tamran/Team-Hydra-II/2-14-17/blueVsConc.png

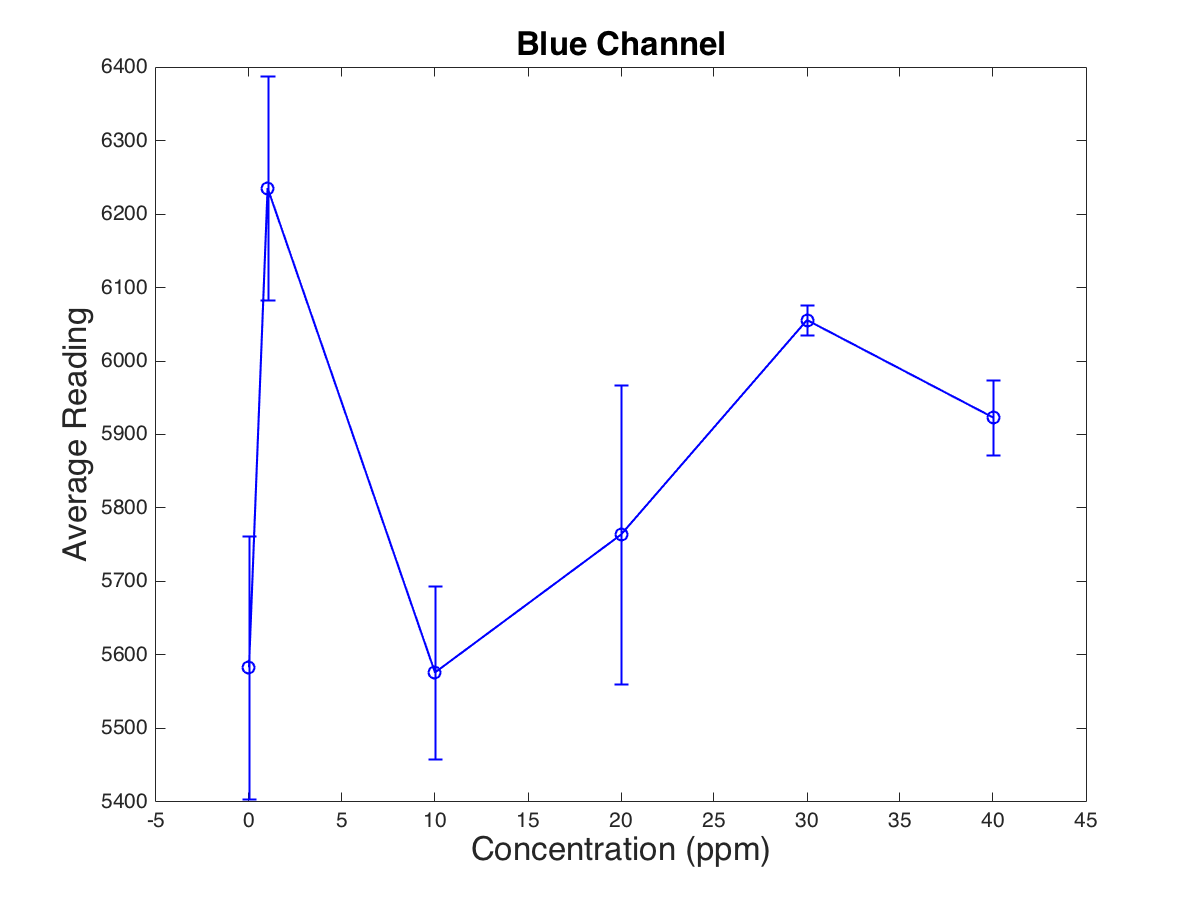
2-14-17/blueVsConc.png
