tamran/Team-Hydra-II/2-14-17/blueVsTime.png

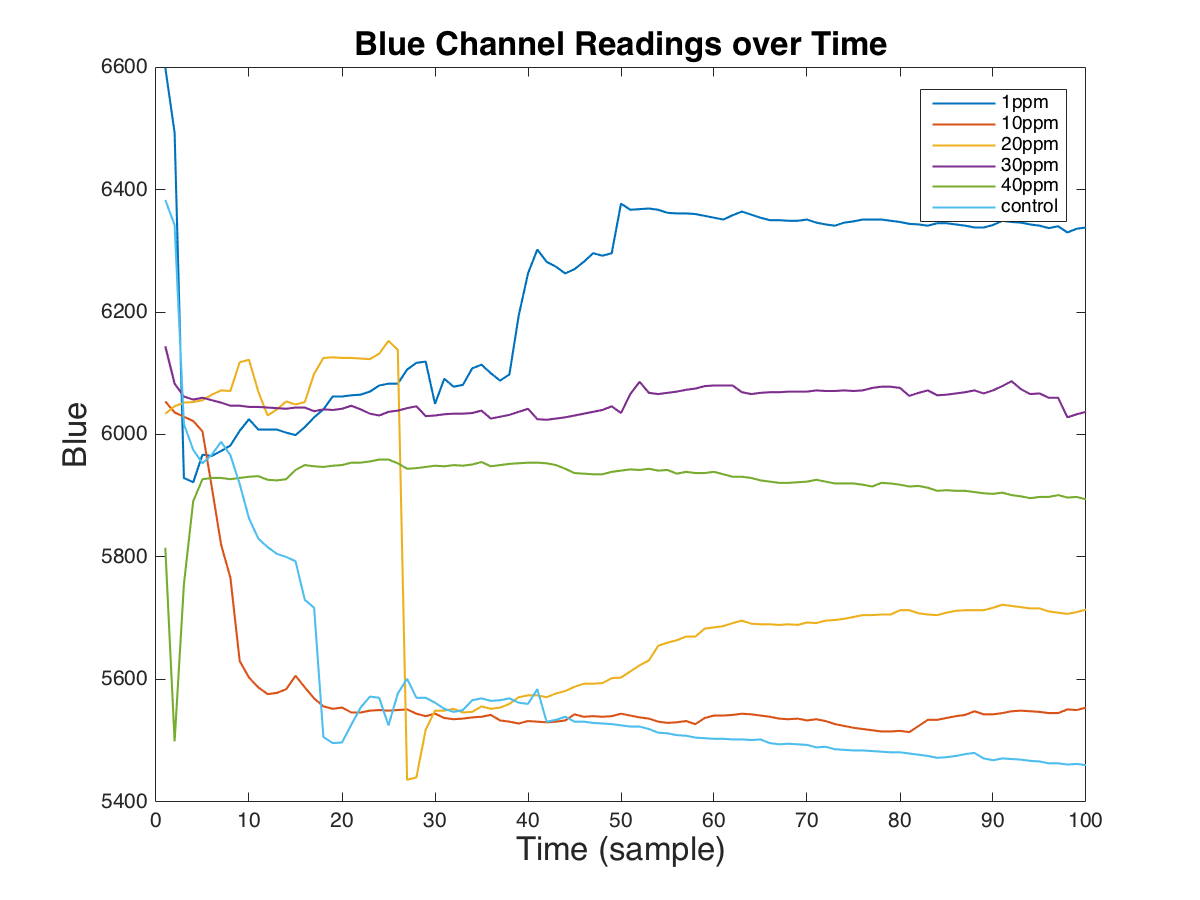
2-14-17/blueVsTime.png
