tamran/Team-Hydra-II/2-14-17/clearVsConc.png

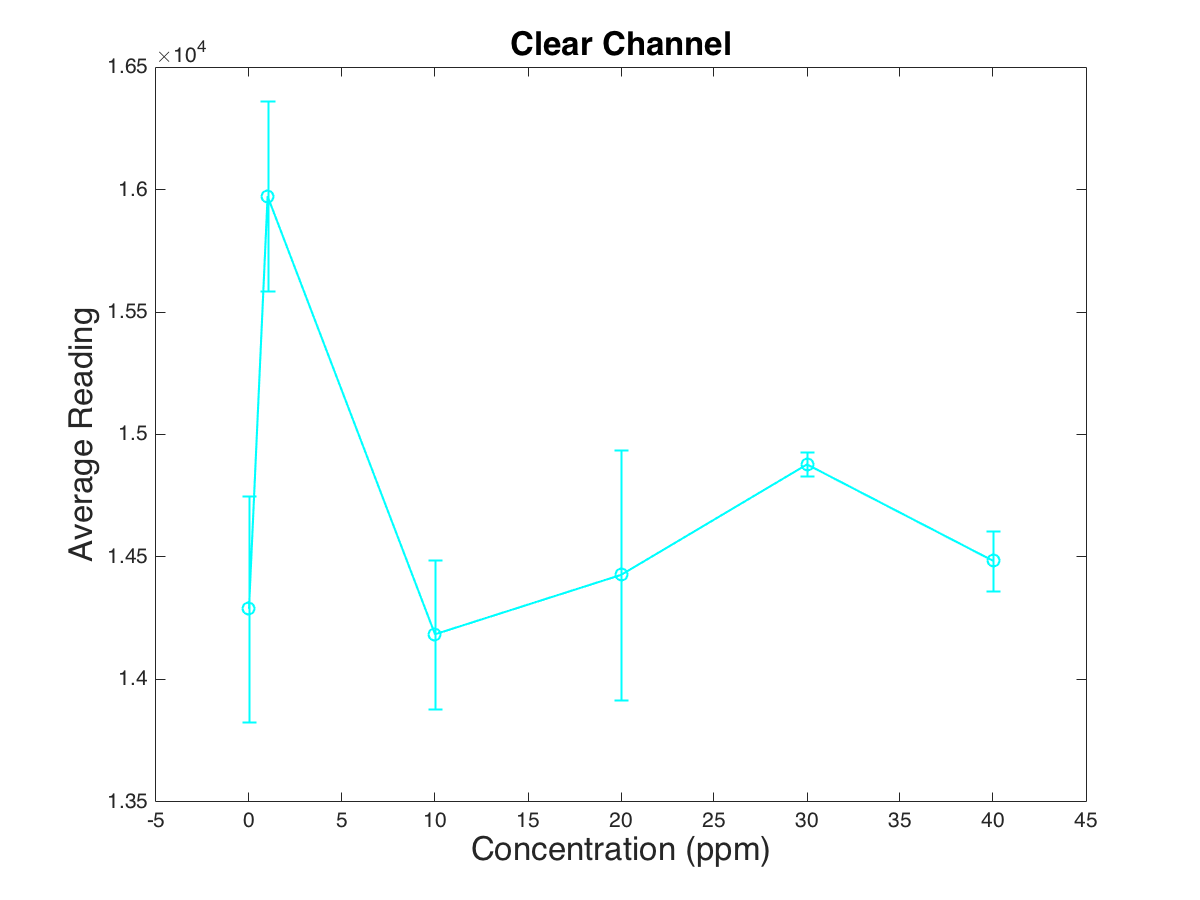
2-14-17/clearVsConc.png
