tamran/Team-Hydra-II/2-14-17/clearVsTime.png

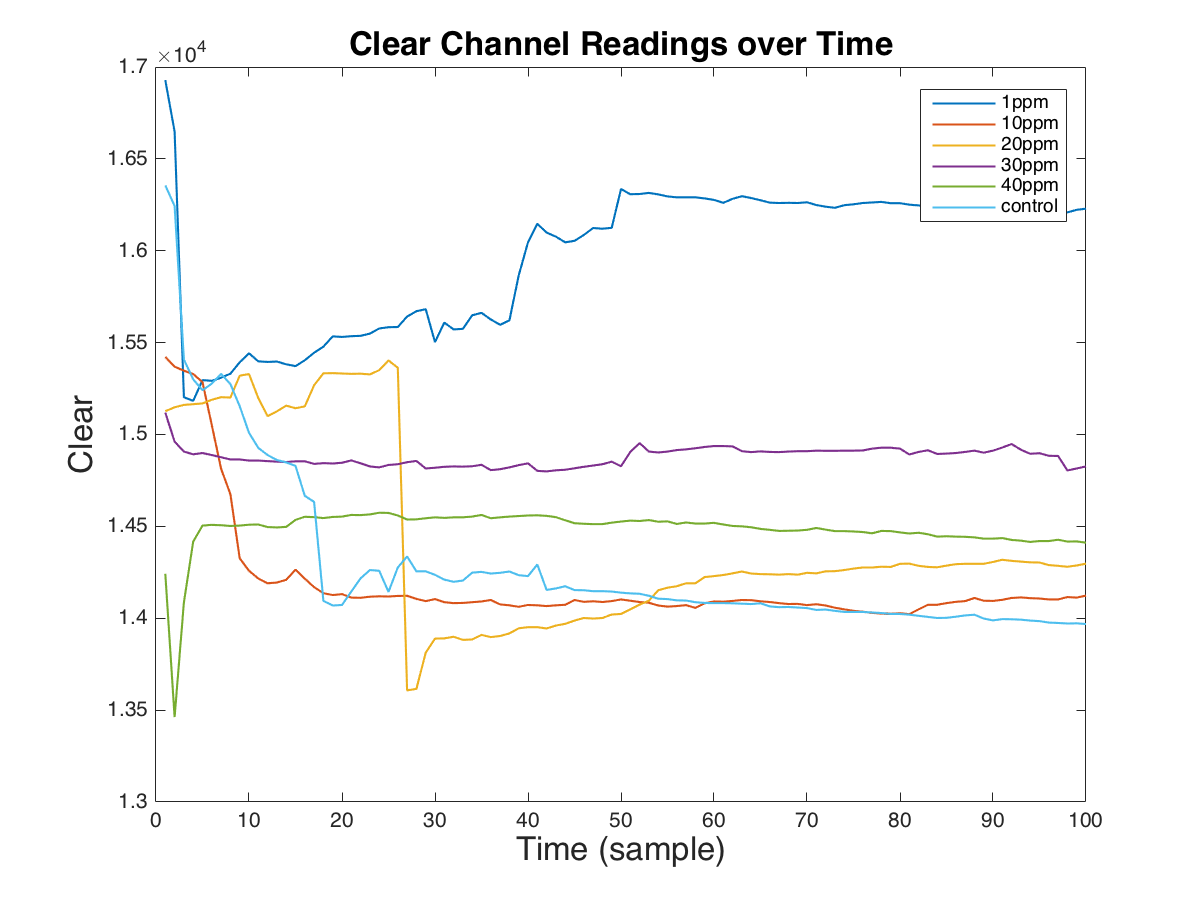
2-14-17/clearVsTime.png
