tamran/Team-Hydra-II/2-14-17/colorTempVsConc.png

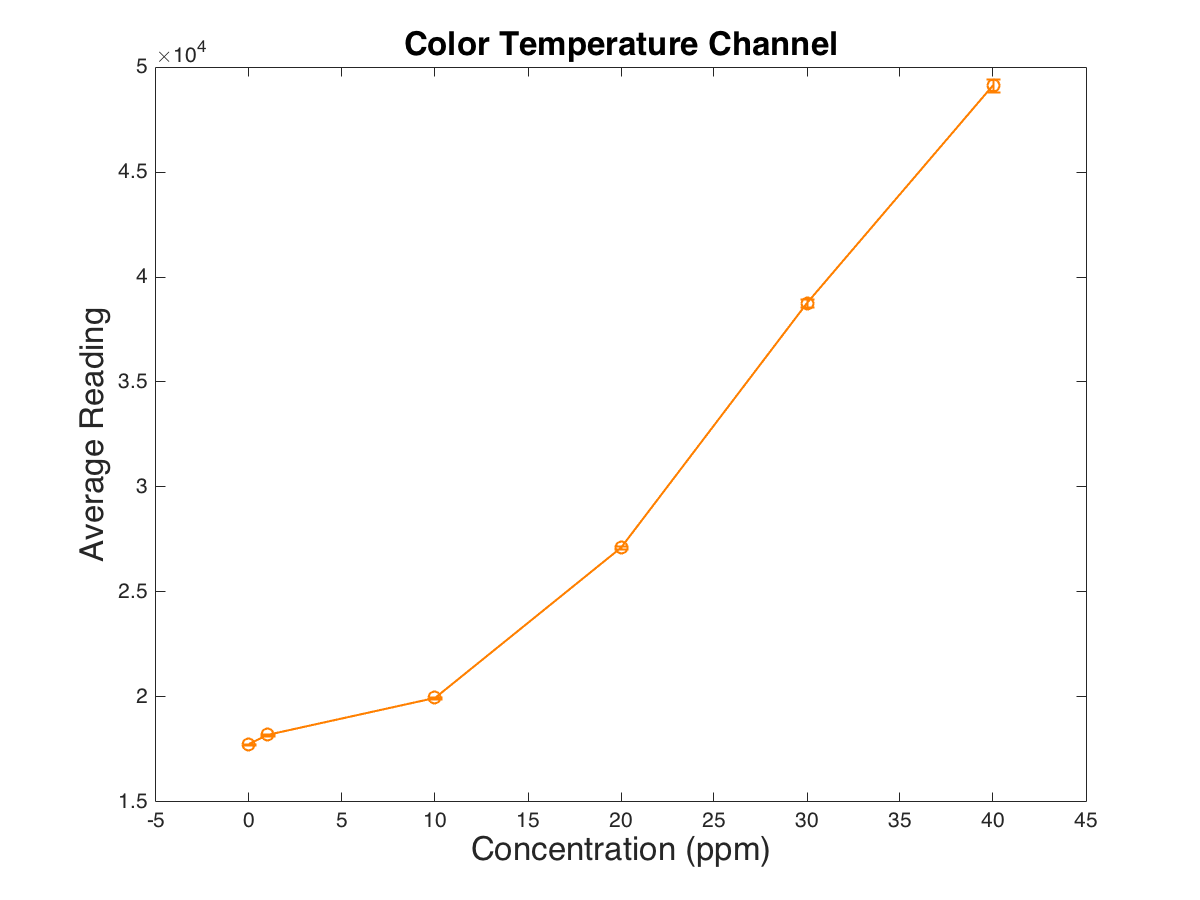
2-14-17/colorTempVsConc.png
