tamran/Team-Hydra-II/2-14-17/cTempVsTime.png

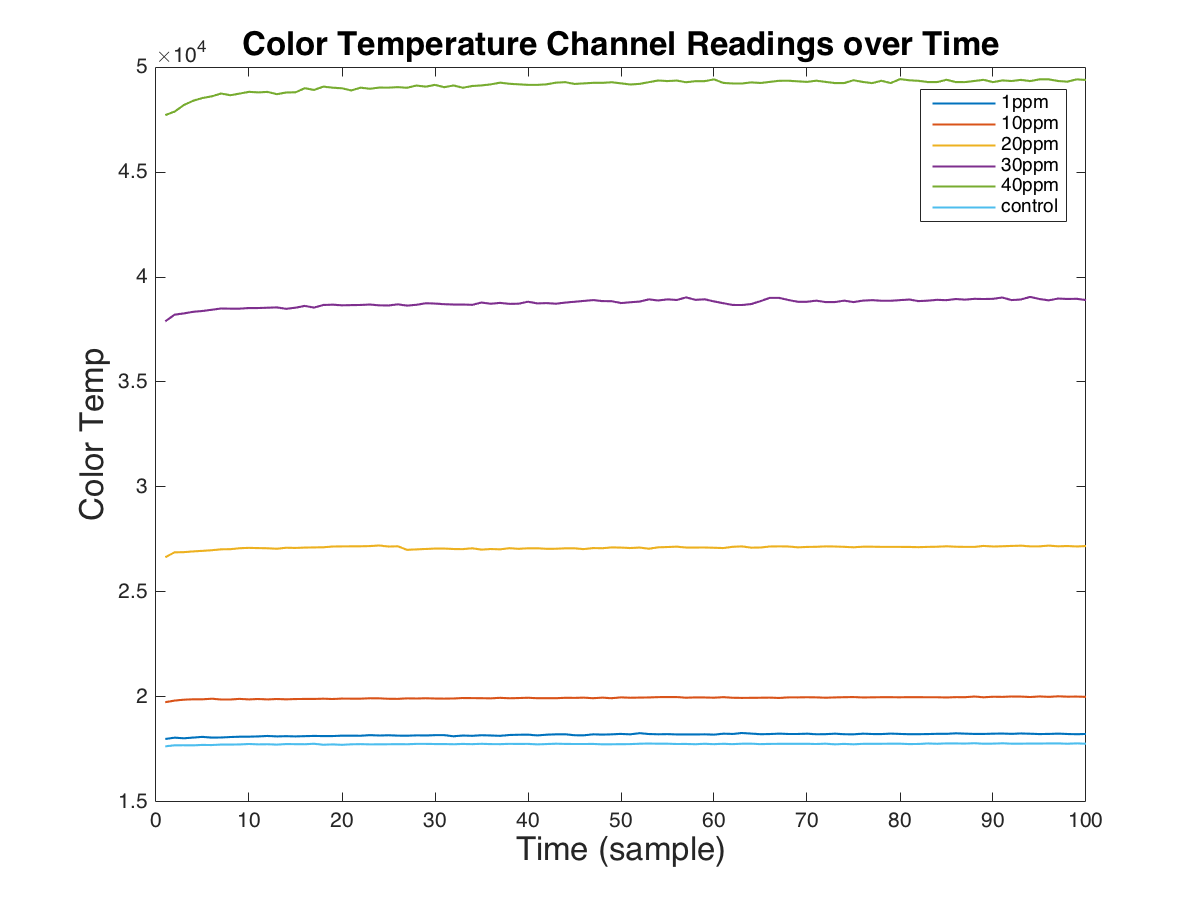
2-14-17/cTempVsTime.png
