tamran/Team-Hydra-II/2-14-17/greenVsConc.png

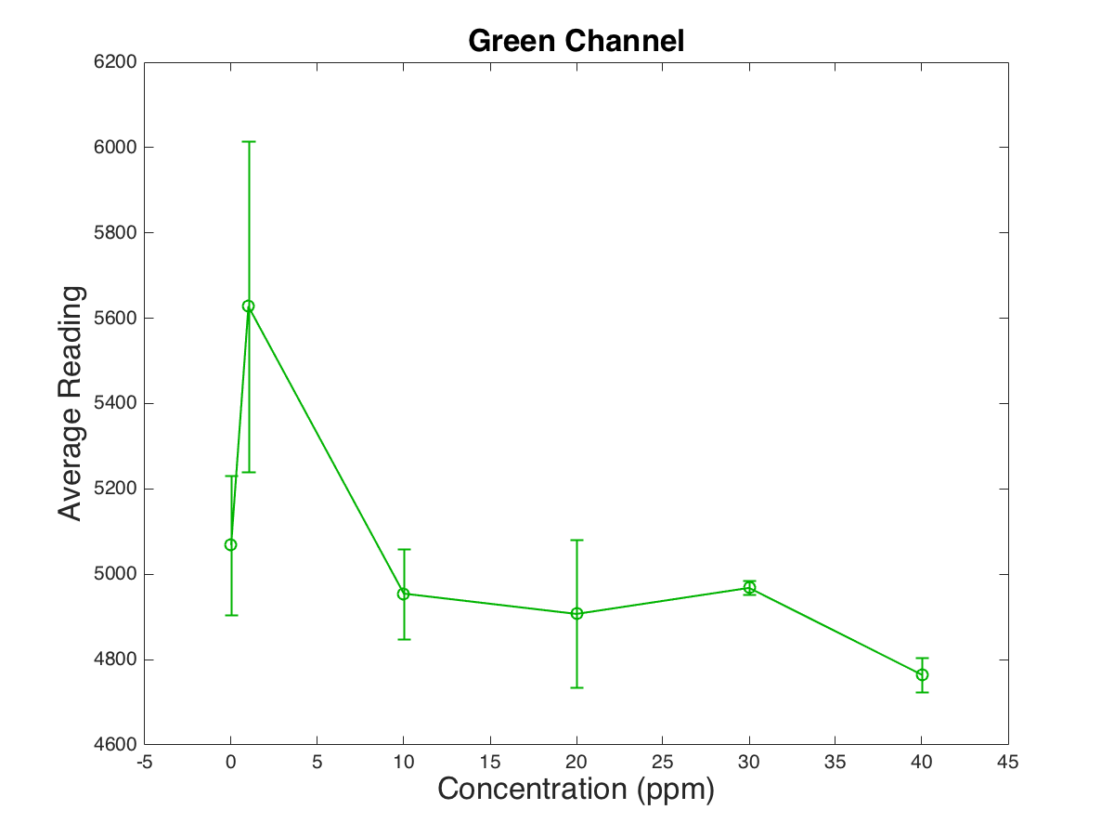
2-14-17/greenVsConc.png
