tamran/Team-Hydra-II/2-14-17/greenVsTime.png

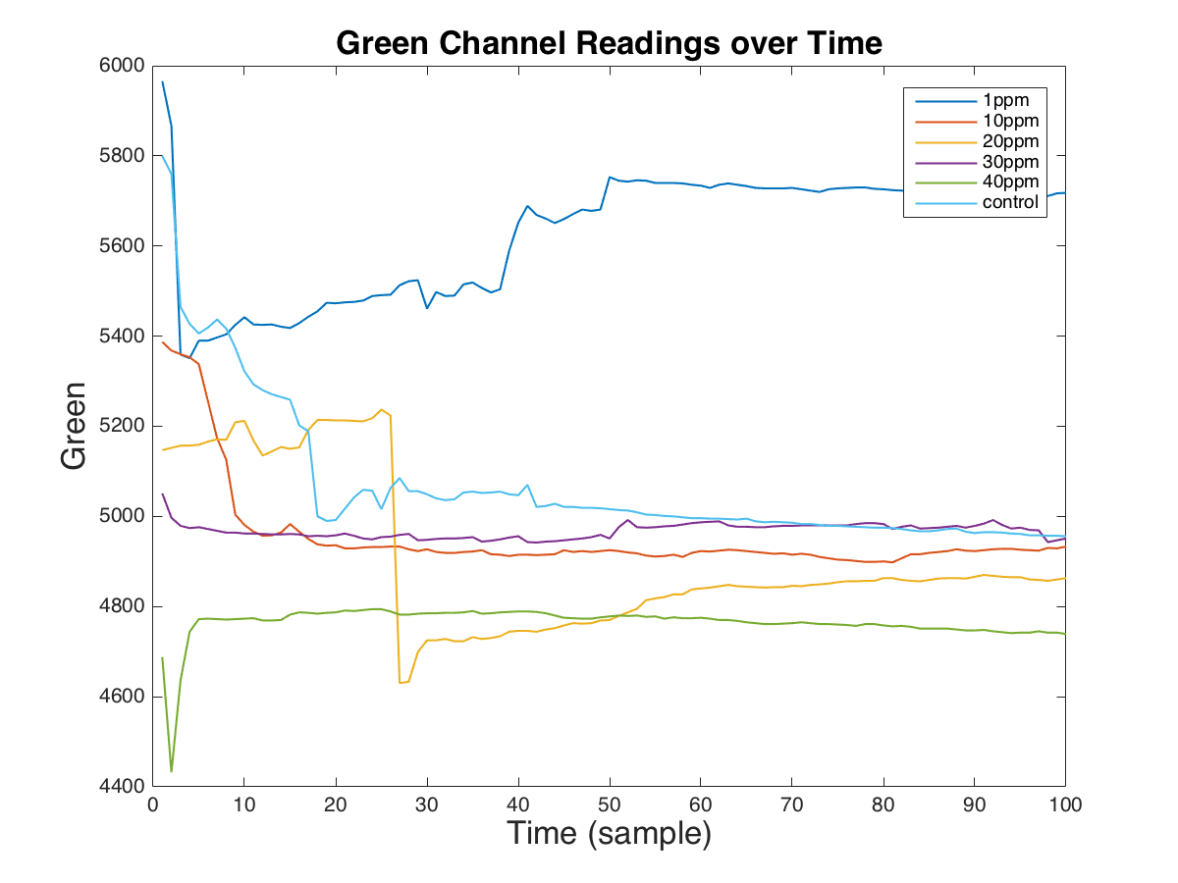
2-14-17/greenVsTime.png
