tamran/Team-Hydra-II/2-14-17/luxVsConc.png

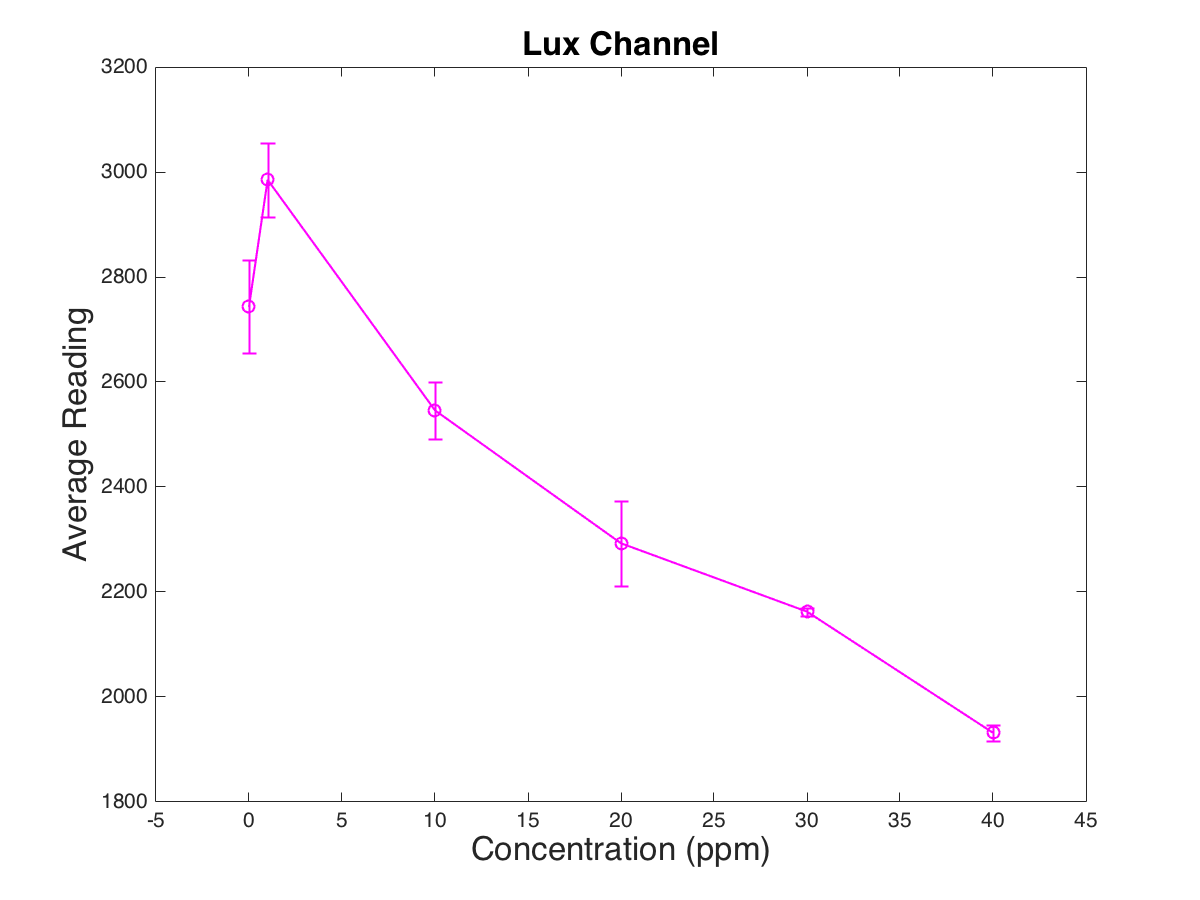
2-14-17/luxVsConc.png
