tamran/Team-Hydra-II/2-14-17/luxVsTime.png

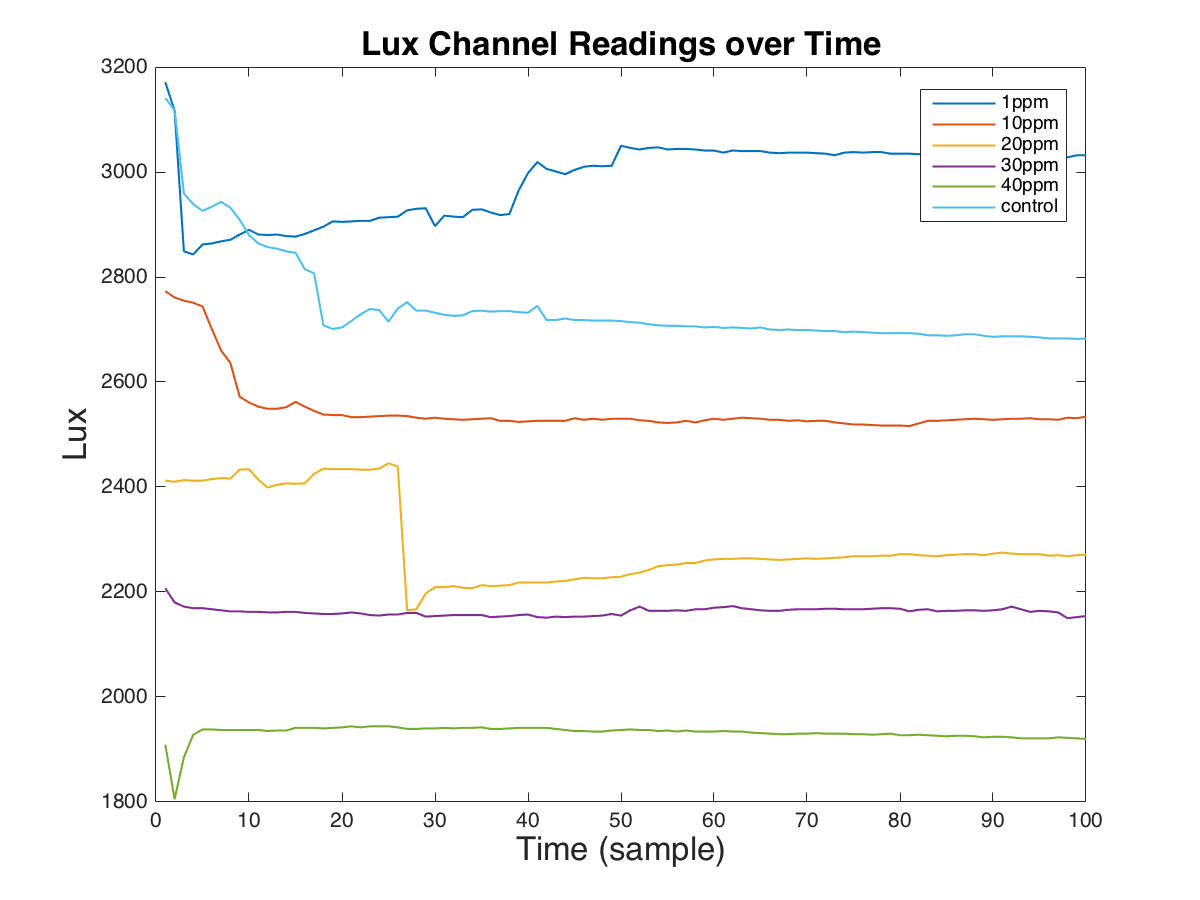
2-14-17/luxVsTime.png
