tamran/Team-Hydra-II/2-14-17/readingVsConc.png

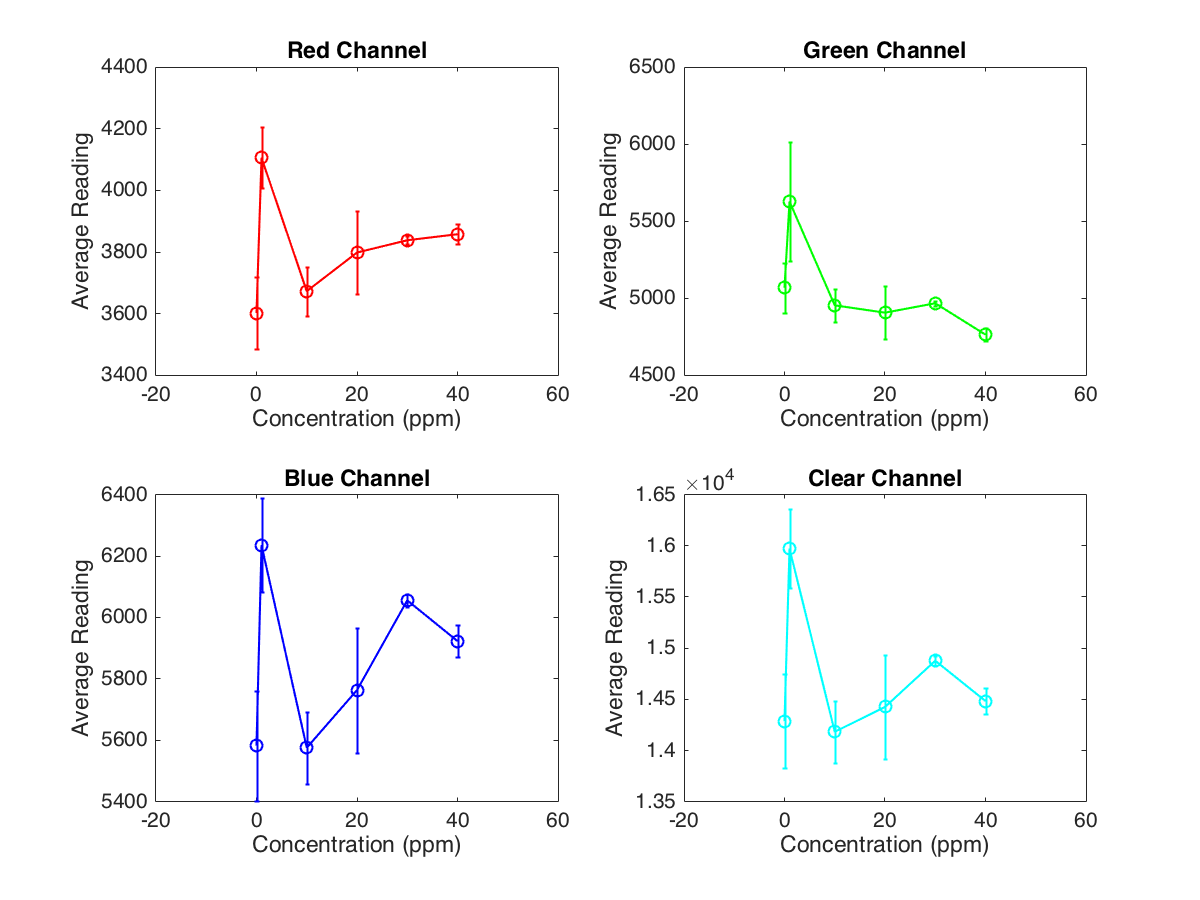
2-14-17/readingVsConc.png
