tamran/Team-Hydra-II/2-14-17/readingVsTime.png

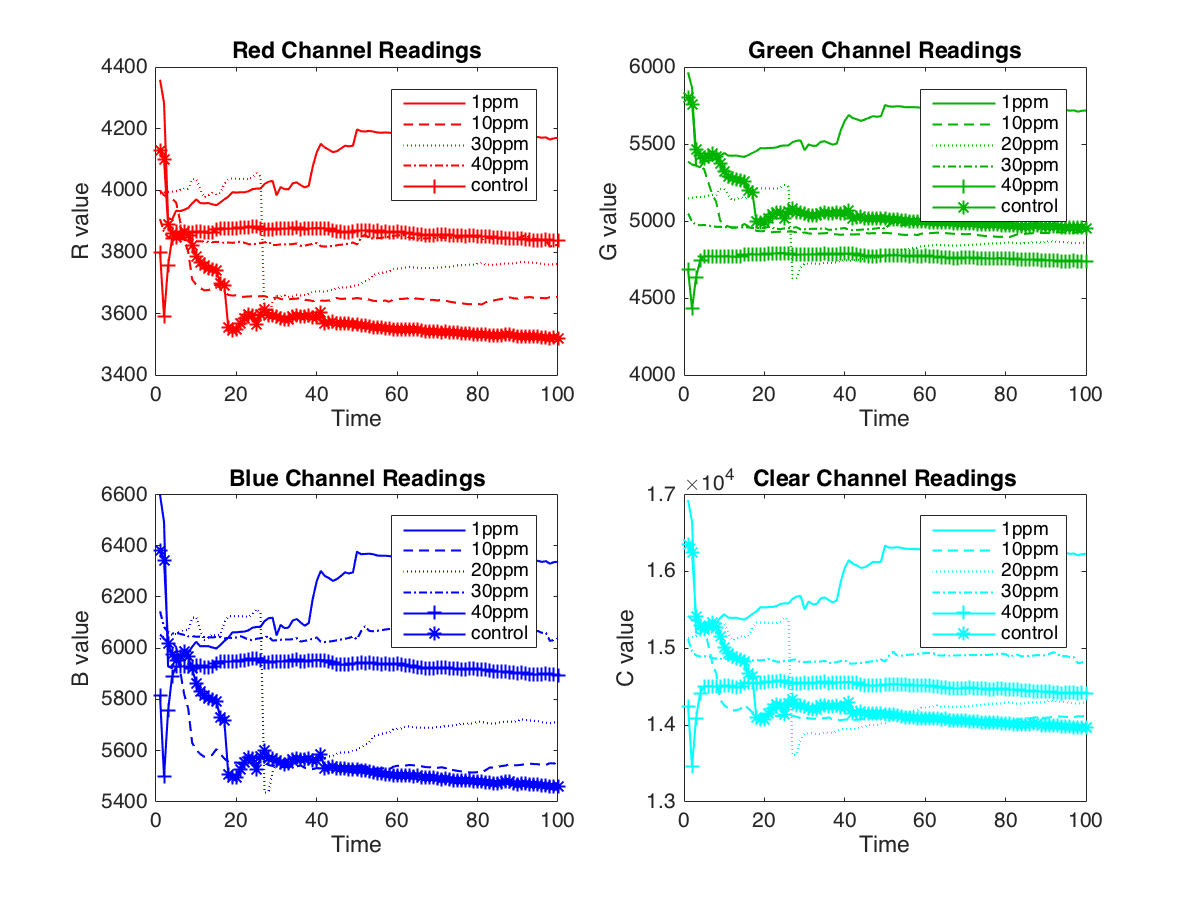
2-14-17/readingVsTime.png
