tamran/Team-Hydra-II/2-14-17/redVsConc.png

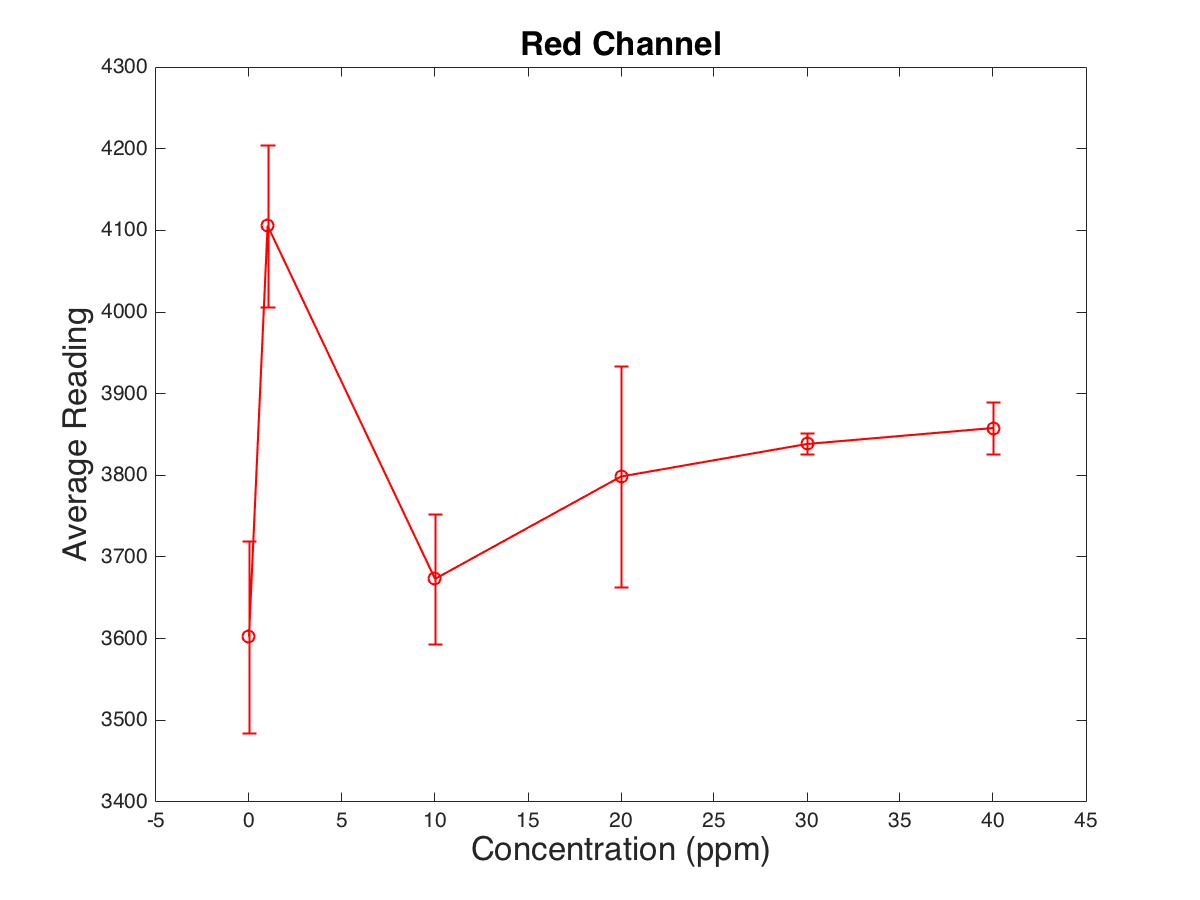
2-14-17/redVsConc.png
