tamran/Team-Hydra-II/2-14-17/redVsTime.png

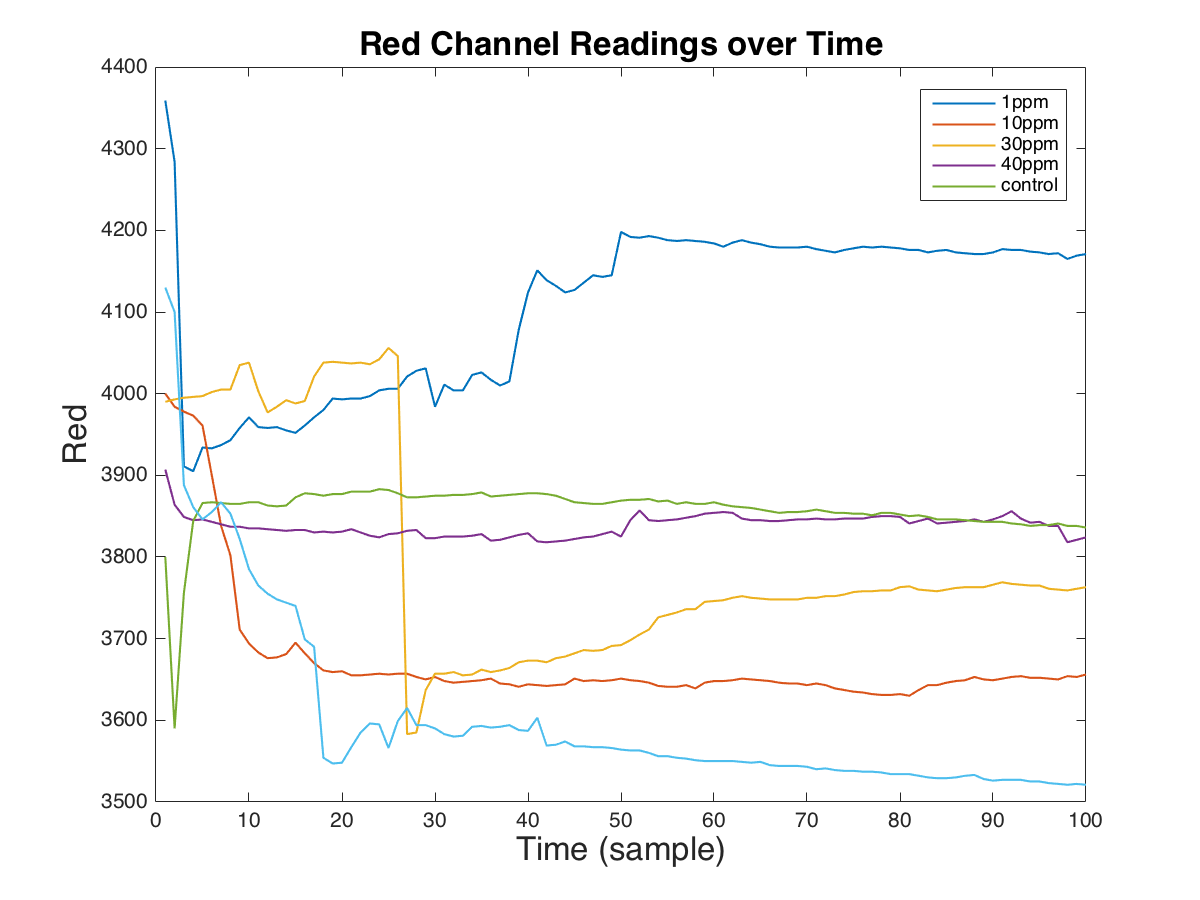
2-14-17/redVsTime.png
