tamran/Team-Hydra-II/initialData/20170215_blue.png

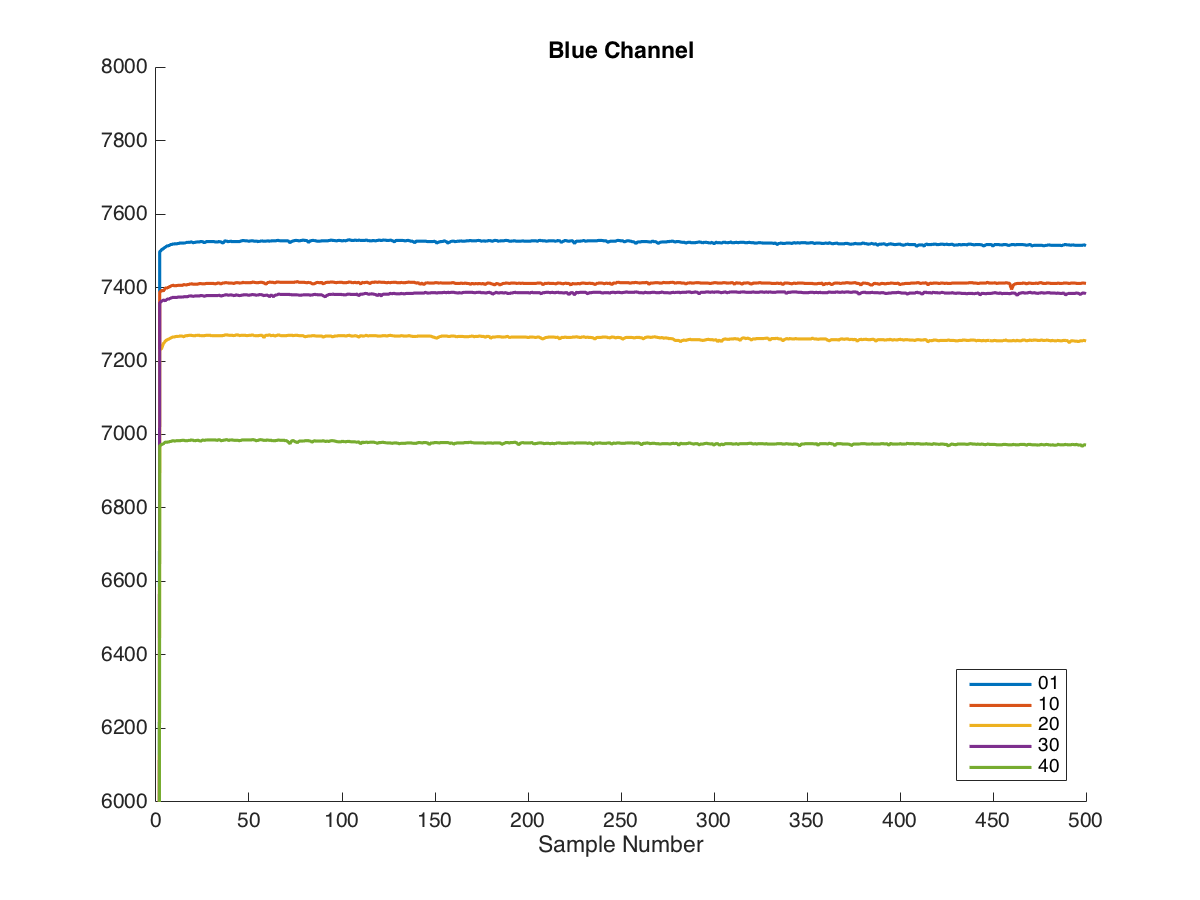
initialData/20170215_blue.png
