tamran/Team-Hydra-II/initialData/20170215_clear.png

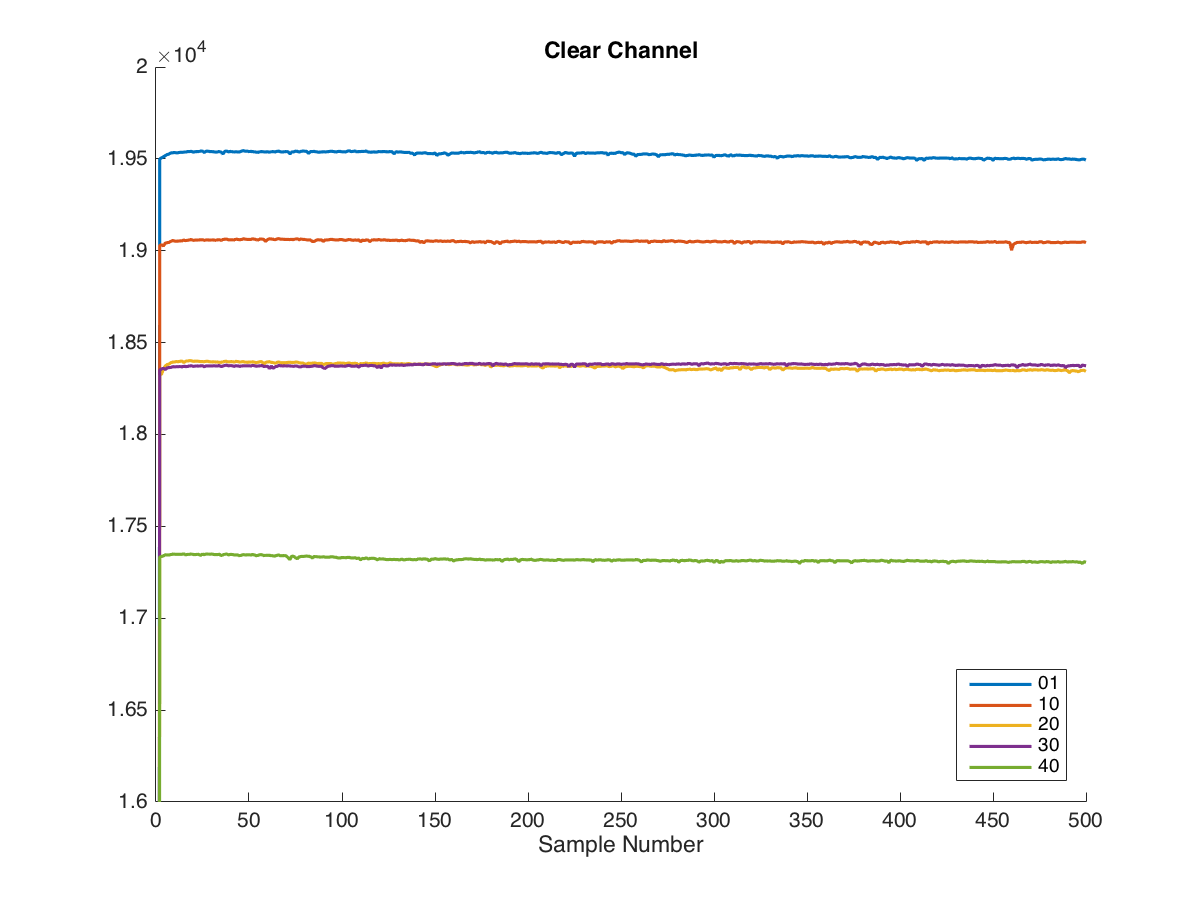
initialData/20170215_clear.png
