tamran/Team-Hydra-II/initialData/20170215_green.png

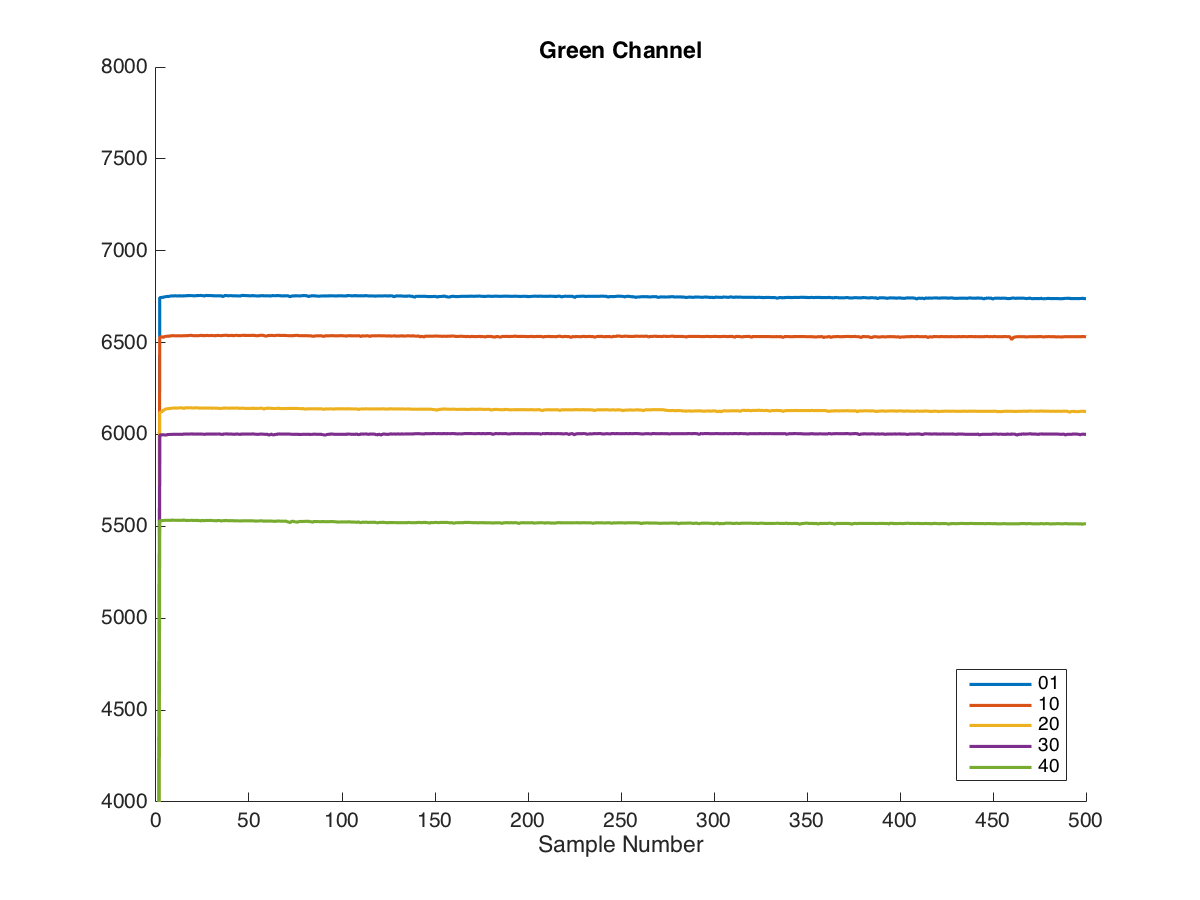
initialData/20170215_green.png
