tamran/Team-Hydra-II/PhotoshopFiles/BodyTopView_CuvetteHolder.png

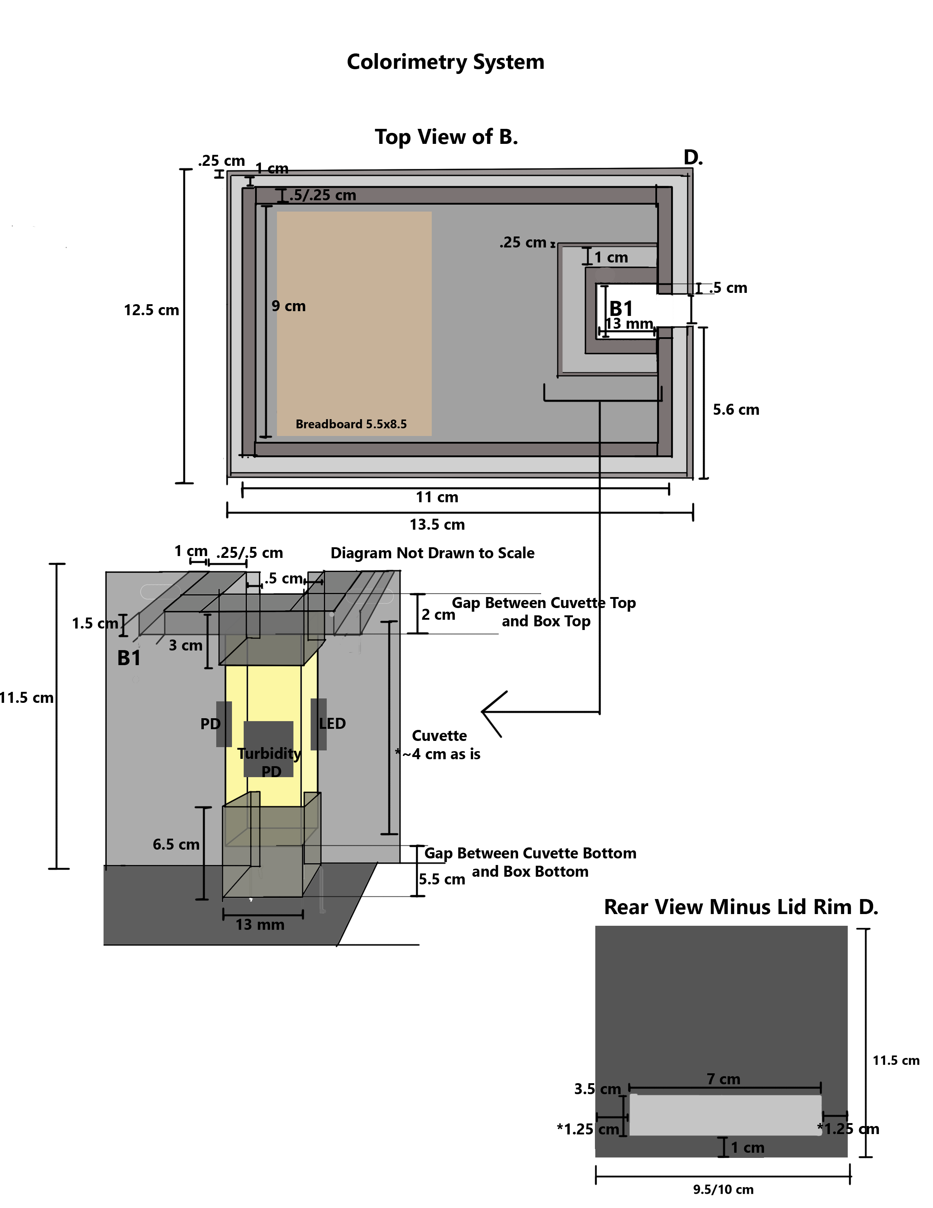
PhotoshopFiles/BodyTopView_CuvetteHolder.png
