tamran/Team-Hydra-II/PhotoshopFiles/Lid.png

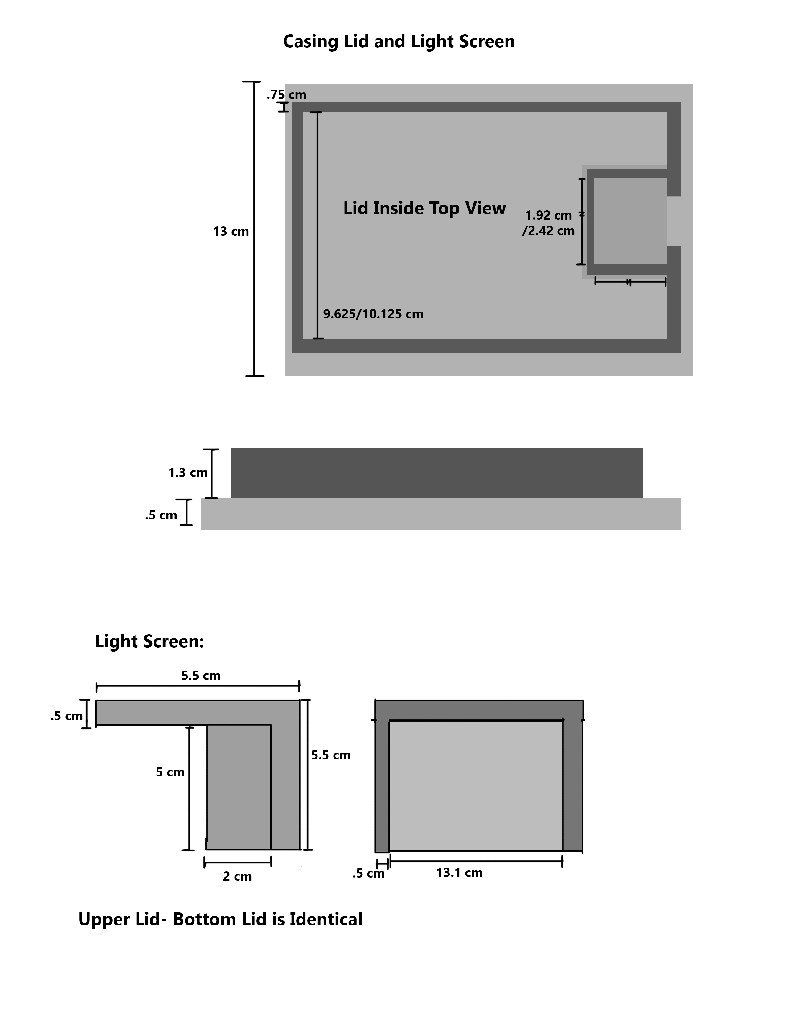
PhotoshopFiles/Lid.png
