tamran/Team-Hydra-II/PhotoshopFiles/phSensor.png

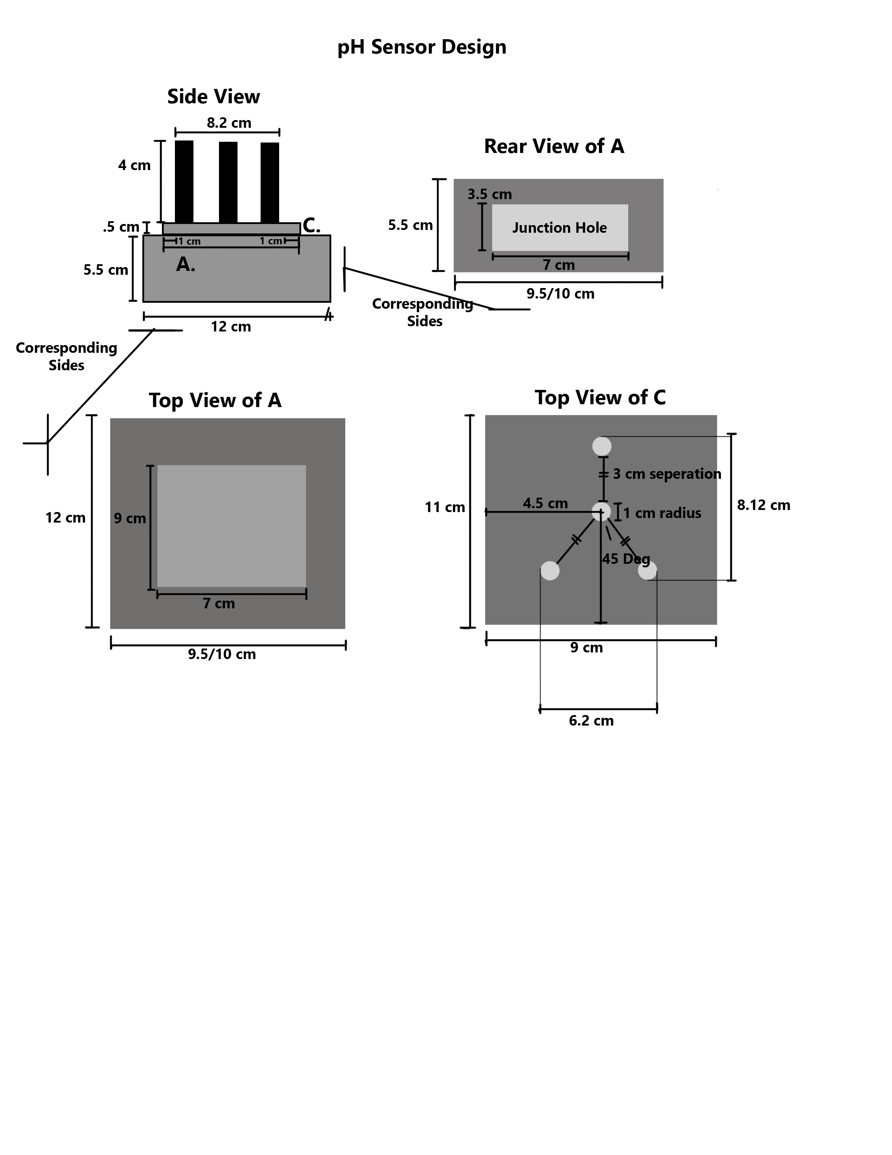
PhotoshopFiles/phSensor.png
