tamran/Team-Hydra-II/pictures/IMG_0730.JPG

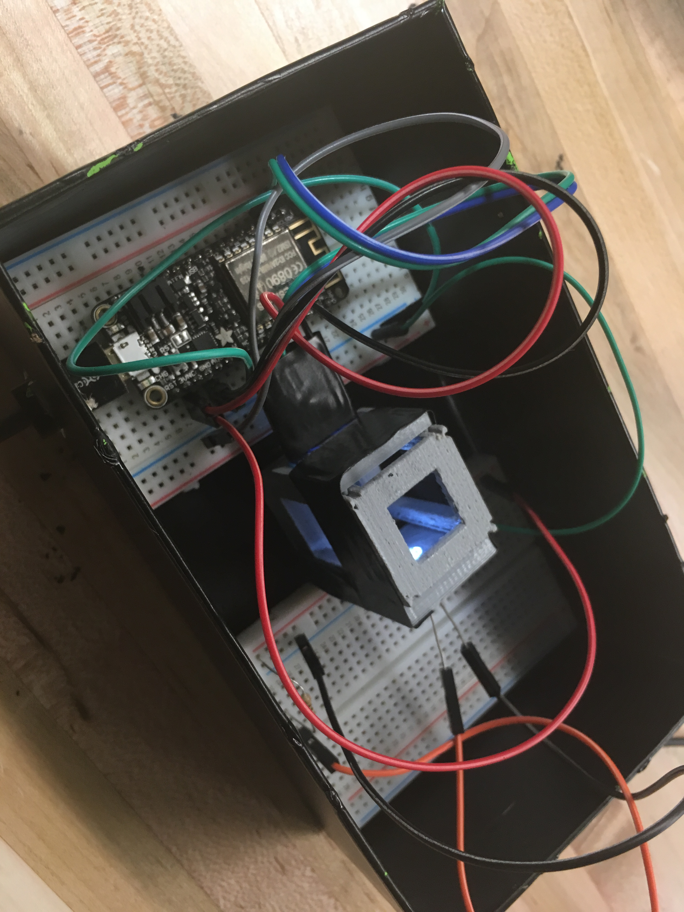
pictures/IMG_0730.JPG
