tamran/Team-Hydra-II/pictures/IMG_0731.JPG

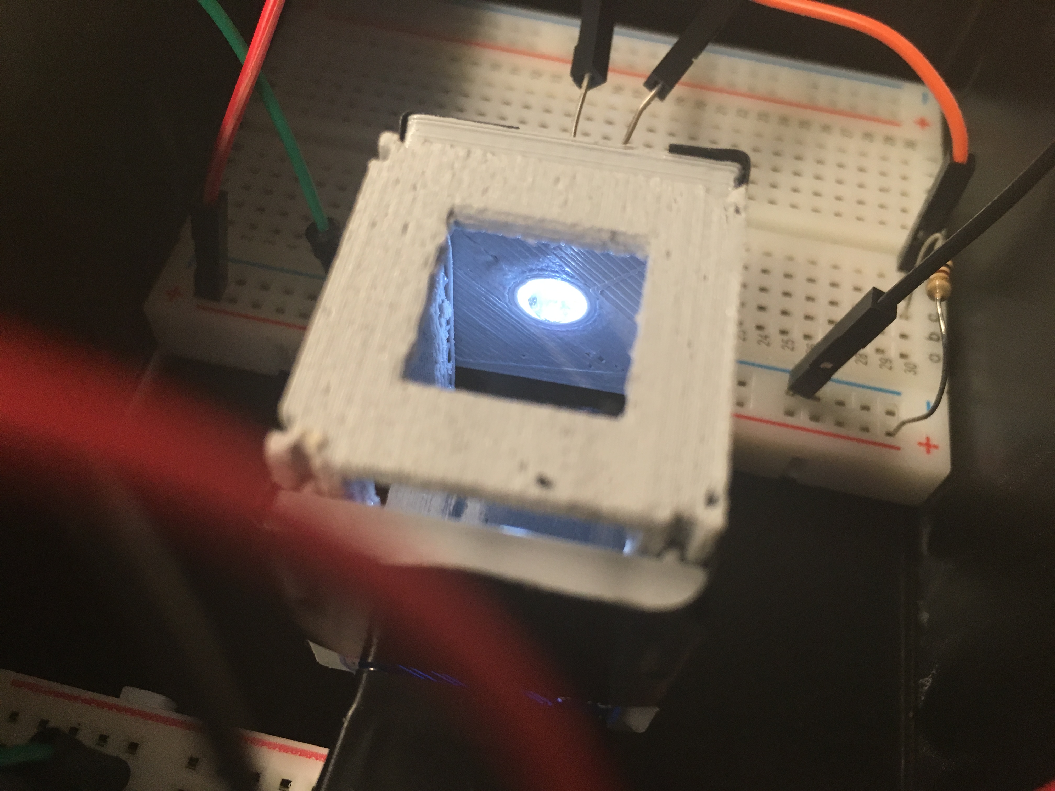
pictures/IMG_0731.JPG
