tamran/Team-Hydra-II/pictures/IMG_0732.JPG

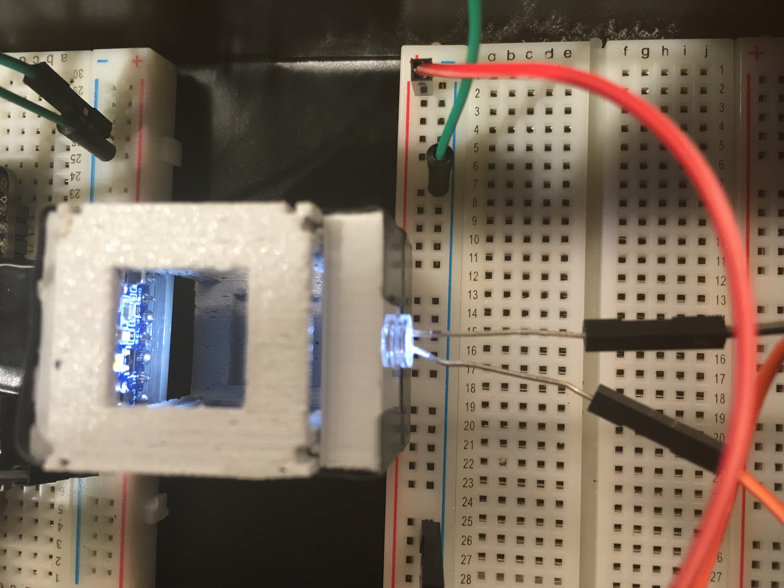
pictures/IMG_0732.JPG
