tamran/Team-Hydra-II/pictures/IMG_0733.JPG

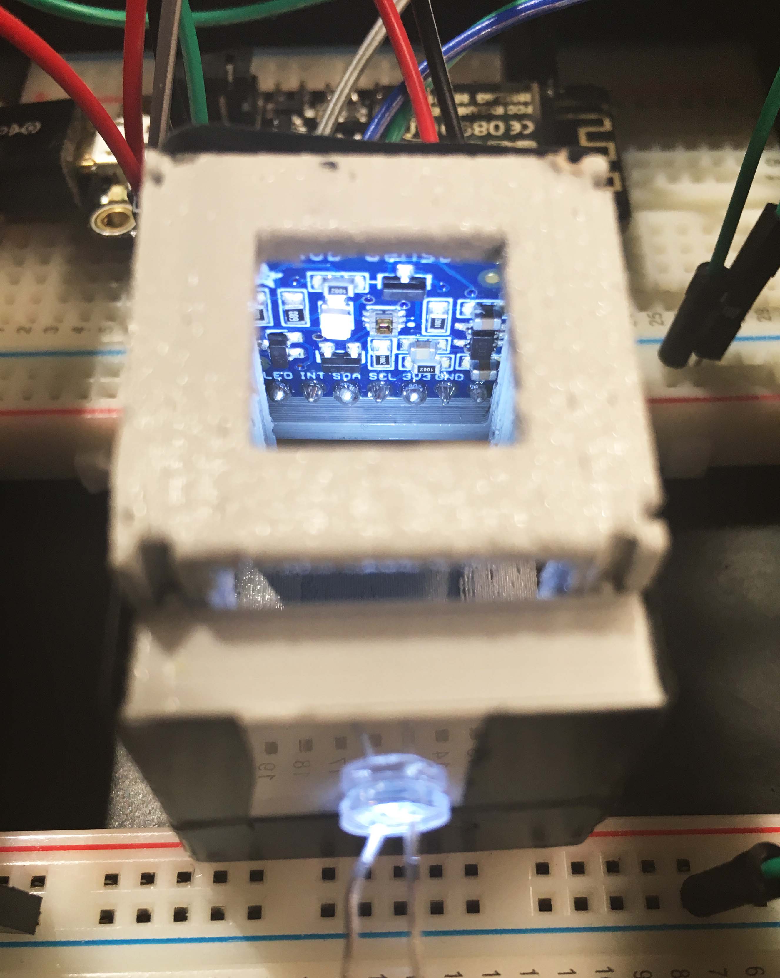
pictures/IMG_0733.JPG
