tamran/Team-Hydra-II/pictures/IMG_0735.JPG

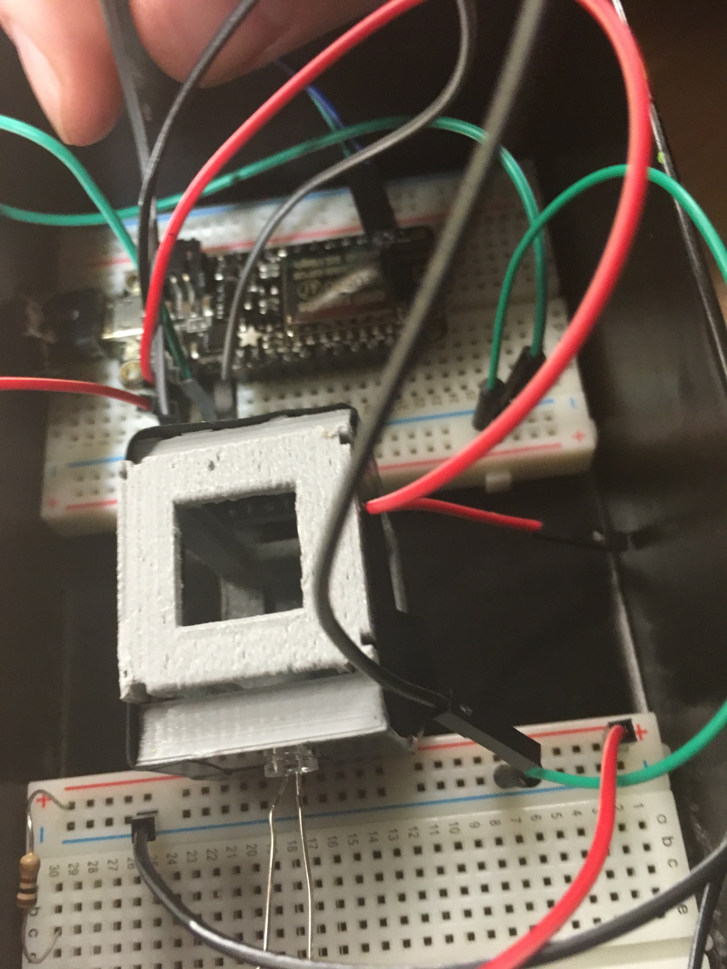
pictures/IMG_0735.JPG
