tamran/Team-Hydra-II/pictures/IMG_0737.JPG

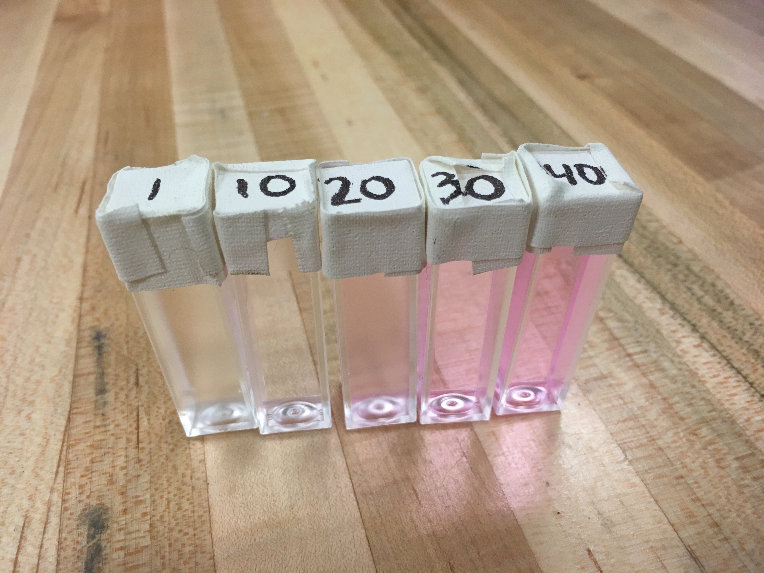
pictures/IMG_0737.JPG
