tamran/Team-Hydra-II/pictures/IMG_0738.JPG

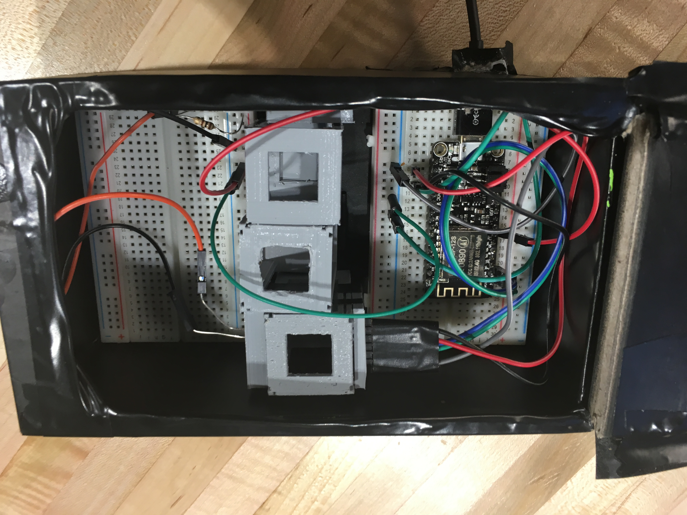
pictures/IMG_0738.JPG
