tamran/Team-Hydra-II/pictures/IMG_0739.JPG

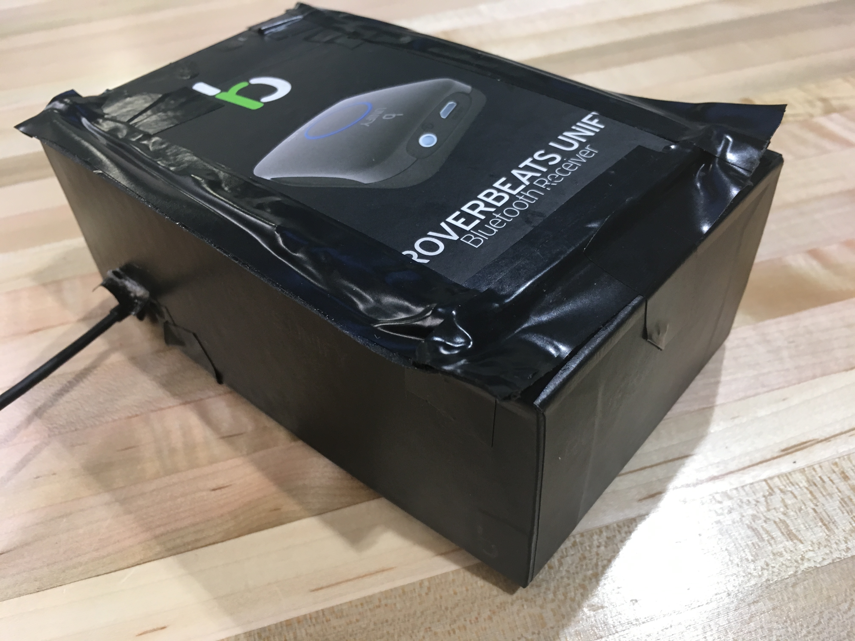
pictures/IMG_0739.JPG
