tamran/Team-Hydra-II/3:22 - Colorimeter Repeatability/colorTest_1ppm_trial1.txt

Color Temp: 19707 K - Lux: 2763 - R: 4025 G: 5385 B: 6052 C: 15589  
Color Temp: 19768 K - Lux: 2762 - R: 4025 G: 5387 B: 6057 C: 15595  
Color Temp: 19825 K - Lux: 2762 - R: 4027 G: 5390 B: 6063 C: 15606  
Color Temp: 19842 K - Lux: 2763 - R: 4028 G: 5392 B: 6066 C: 15612  
Color Temp: 19864 K - Lux: 2762 - R: 4028 G: 5392 B: 6067 C: 15613  
Color Temp: 19885 K - Lux: 2761 - R: 4028 G: 5392 B: 6068 C: 15614  
Color Temp: 19885 K - Lux: 2761 - R: 4028 G: 5392 B: 6068 C: 15615  
Color Temp: 19885 K - Lux: 2761 - R: 4028 G: 5392 B: 6068 C: 15615  
Color Temp: 19924 K - Lux: 2761 - R: 4029 G: 5394 B: 6072 C: 15621  
Color Temp: 19924 K - Lux: 2761 - R: 4029 G: 5394 B: 6072 C: 15621  
Color Temp: 19924 K - Lux: 2761 - R: 4029 G: 5394 B: 6072 C: 15621  
Color Temp: 19924 K - Lux: 2761 - R: 4029 G: 5394 B: 6072 C: 15620  
Color Temp: 19924 K - Lux: 2761 - R: 4029 G: 5394 B: 6072 C: 15621  
Color Temp: 19926 K - Lux: 2761 - R: 4028 G: 5394 B: 6072 C: 15620  
Color Temp: 19946 K - Lux: 2760 - R: 4029 G: 5394 B: 6073 C: 15621  
Color Temp: 19946 K - Lux: 2760 - R: 4029 G: 5394 B: 6073 C: 15621  
Color Temp: 19944 K - Lux: 2761 - R: 4029 G: 5395 B: 6074 C: 15624  
Color Temp: 19941 K - Lux: 2762 - R: 4030 G: 5396 B: 6075 C: 15627  
Color Temp: 19956 K - Lux: 2762 - R: 4032 G: 5398 B: 6078 C: 15635  
Color Temp: 19955 K - Lux: 2763 - R: 4032 G: 5399 B: 6079 C: 15636  
Color Temp: 19955 K - Lux: 2763 - R: 4032 G: 5399 B: 6079 C: 15636  
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
Color Temp: 20264 K - Lux: 3157 - R: 4624 G: 6192 B: 6988 C: 17952  
Color Temp: 20283 K - Lux: 3156 - R: 4624 G: 6192 B: 6989 C: 17952  
Color Temp: 20283 K - Lux: 3156 - R: 4624 G: 6192 B: 6989 C: 17952  
Color Temp: 20282 K - Lux: 3156 - R: 4625 G: 6192 B: 6989 C: 17954
