tamran/Team-Hydra-II/2-15-17(control)/colorTest_control.txt

Color Temp: 17847 K - Lux: 3467 - R: 4872 G: 6565 B: 7259 C: 18876  
Color Temp: 17915 K - Lux: 3462 - R: 4867 G: 6561 B: 7259 C: 18867  
Color Temp: 17953 K - Lux: 3462 - R: 4870 G: 6565 B: 7266 C: 18880  
Color Temp: 17983 K - Lux: 3461 - R: 4870 G: 6565 B: 7268 C: 18883  
Color Temp: 17989 K - Lux: 3459 - R: 4867 G: 6562 B: 7265 C: 18874  
Color Temp: 17995 K - Lux: 3462 - R: 4871 G: 6568 B: 7272 C: 18889  
Color Temp: 18027 K - Lux: 3460 - R: 4870 G: 6567 B: 7273 C: 18889  
Color Temp: 18029 K - Lux: 3460 - R: 4869 G: 6566 B: 7272 C: 18886  
Color Temp: 18044 K - Lux: 3459 - R: 4869 G: 6566 B: 7273 C: 18889  
Color Temp: 18044 K - Lux: 3460 - R: 4869 G: 6567 B: 7274 C: 18890  
Color Temp: 18042 K - Lux: 3460 - R: 4870 G: 6568 B: 7275 C: 18894  
Color Temp: 18055 K - Lux: 3460 - R: 4871 G: 6569 B: 7277 C: 18899  
Color Temp: 18053 K - Lux: 3461 - R: 4872 G: 6570 B: 7278 C: 18900  
Color Temp: 18053 K - Lux: 3461 - R: 4872 G: 6570 B: 7278 C: 18900  
Color Temp: 18067 K - Lux: 3461 - R: 4872 G: 6571 B: 7280 C: 18903  
Color Temp: 18079 K - Lux: 3460 - R: 4874 G: 6572 B: 7282 C: 18909  
Color Temp: 18095 K - Lux: 3460 - R: 4873 G: 6572 B: 7283 C: 18909  
Color Temp: 18078 K - Lux: 3462 - R: 4874 G: 6574 B: 7284 C: 18912  
Color Temp: 18093 K - Lux: 3461 - R: 4874 G: 6574 B: 7285 C: 18913  
Color Temp: 18093 K - Lux: 3461 - R: 4874 G: 6574 B: 7285 C: 18913  
Color Temp: 18084 K - Lux: 3461 - R: 4871 G: 6571 B: 7281 C: 18903  
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
Color Temp: 18281 K - Lux: 3468 - R: 4890 G: 6601 B: 7327 C: 18997  
Color Temp: 18281 K - Lux: 3468 - R: 4890 G: 6601 B: 7327 C: 18997  
Color Temp: 18279 K - Lux: 3469 - R: 4891 G: 6602 B: 7328 C: 19001  
Color Temp: 18282 K - Lux: 3467 - R: 4890 G: 6600 B: 7326 C: 18997
