tamran/Team-Hydra-II/2-3-17/colorTest_g_10ppm.txt

Color Temp: 5643 K - Lux: 674 - R: 368 G: 725 B: 478 C: 1620  
Color Temp: 5651 K - Lux: 670 - R: 366 G: 721 B: 476 C: 1612  
Color Temp: 5650 K - Lux: 675 - R: 368 G: 726 B: 479 C: 1623  
Color Temp: 5637 K - Lux: 676 - R: 368 G: 726 B: 478 C: 1621  
Color Temp: 5652 K - Lux: 680 - R: 368 G: 730 B: 481 C: 1628  
Color Temp: 5654 K - Lux: 681 - R: 369 G: 731 B: 482 C: 1631  
Color Temp: 5654 K - Lux: 681 - R: 369 G: 731 B: 482 C: 1631  
Color Temp: 5643 K - Lux: 674 - R: 368 G: 725 B: 478 C: 1621  
Color Temp: 5646 K - Lux: 677 - R: 369 G: 728 B: 480 C: 1626  
Color Temp: 5647 K - Lux: 680 - R: 369 G: 730 B: 481 C: 1628  
Color Temp: 5645 K - Lux: 679 - R: 368 G: 729 B: 480 C: 1626  
Color Temp: 5638 K - Lux: 667 - R: 367 G: 718 B: 474 C: 1608  
Color Temp: 5647 K - Lux: 672 - R: 367 G: 723 B: 477 C: 1616  
Color Temp: 5636 K - Lux: 674 - R: 368 G: 724 B: 477 C: 1618  
Color Temp: 5638 K - Lux: 667 - R: 367 G: 718 B: 474 C: 1608  
Color Temp: 5644 K - Lux: 677 - R: 368 G: 727 B: 479 C: 1624  
Color Temp: 5658 K - Lux: 679 - R: 368 G: 729 B: 481 C: 1627  
Color Temp: 5645 K - Lux: 679 - R: 368 G: 729 B: 480 C: 1627  
Color Temp: 5641 K - Lux: 681 - R: 369 G: 731 B: 481 C: 1630  
Color Temp: 5648 K - Lux: 682 - R: 369 G: 732 B: 482 C: 1632  
Color Temp: 5654 K - Lux: 681 - R: 369 G: 731 B: 482 C: 1631  
Color Temp: 5643 K - Lux: 674 - R: 368 G: 725 B: 478 C: 1621  
Color Temp: 5635 K - Lux: 671 - R: 368 G: 722 B: 476 C: 1616  
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
Color Temp: 5654 K - Lux: 681 - R: 369 G: 731 B: 482 C: 1631  
Color Temp: 5655 K - Lux: 683 - R: 369 G: 733 B: 483 C: 1633  
Color Temp: 5655 K - Lux: 683 - R: 369 G: 733 B: 483 C: 1633  
Color Temp: 5649 K - Lux: 685 - R: 369 G: 734 B: 483 C: 1635  
Color Temp: 5649 K - Lux: 685 - R: 369 G: 734 B: 483 C: 1635  
Color Temp: 5655 K - Lux: 683 - R: 369 G: 733 B: 483 C: 1634  
Color Temp: 5655 K - Lux: 683 - R: 369 G: 733 B: 483 C: 1634  
Color Temp: 5655 K - Lux: 683 - R: 369 G: 733 B: 483 C: 1633  
Color Temp: 5649 K - Lux: 685 - R: 369 G: 734 B: 483 C: 1635  
Color Temp: 5662 K - Lux: 684 - R: 369 G: 734 B: 484 C: 1636
