tamran/Team-Hydra-II/2-3-17/colorTest_g_1ppm.txt

Color Temp: 5590 K - Lux: 646 - R: 356 G: 694 B: 455 C: 1541  
Color Temp: 5590 K - Lux: 646 - R: 356 G: 694 B: 455 C: 1542  
Color Temp: 5579 K - Lux: 648 - R: 357 G: 695 B: 455 C: 1543  
Color Temp: 5579 K - Lux: 648 - R: 357 G: 695 B: 455 C: 1543  
Color Temp: 5585 K - Lux: 648 - R: 356 G: 695 B: 455 C: 1542  
Color Temp: 5585 K - Lux: 648 - R: 356 G: 695 B: 455 C: 1542  
Color Temp: 5579 K - Lux: 648 - R: 357 G: 695 B: 455 C: 1543  
Color Temp: 5579 K - Lux: 648 - R: 357 G: 695 B: 455 C: 1543  
Color Temp: 5585 K - Lux: 648 - R: 356 G: 695 B: 455 C: 1542  
Color Temp: 5579 K - Lux: 648 - R: 357 G: 695 B: 455 C: 1542  
Color Temp: 5579 K - Lux: 648 - R: 357 G: 695 B: 455 C: 1543  
Color Temp: 5579 K - Lux: 648 - R: 357 G: 695 B: 455 C: 1543  
Color Temp: 5585 K - Lux: 648 - R: 356 G: 695 B: 455 C: 1542  
Color Temp: 5585 K - Lux: 648 - R: 356 G: 695 B: 455 C: 1542  
Color Temp: 5579 K - Lux: 648 - R: 357 G: 695 B: 455 C: 1543  
Color Temp: 5579 K - Lux: 648 - R: 357 G: 695 B: 455 C: 1543  
Color Temp: 5585 K - Lux: 648 - R: 356 G: 695 B: 455 C: 1542  
Color Temp: 5579 K - Lux: 648 - R: 357 G: 695 B: 455 C: 1543  
Color Temp: 5579 K - Lux: 648 - R: 357 G: 695 B: 455 C: 1543  
Color Temp: 5579 K - Lux: 648 - R: 357 G: 695 B: 455 C: 1542  
Color Temp: 5585 K - Lux: 648 - R: 356 G: 695 B: 455 C: 1542  
Color Temp: 5579 K - Lux: 648 - R: 357 G: 695 B: 455 C: 1543  
Color Temp: 5579 K - Lux: 648 - R: 357 G: 695 B: 455 C: 1543  
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
Color Temp: 5579 K - Lux: 648 - R: 357 G: 695 B: 455 C: 1543  
Color Temp: 5574 K - Lux: 649 - R: 357 G: 696 B: 455 C: 1543  
Color Temp: 5579 K - Lux: 648 - R: 357 G: 695 B: 455 C: 1543  
Color Temp: 5579 K - Lux: 648 - R: 357 G: 695 B: 455 C: 1543  
Color Temp: 5574 K - Lux: 649 - R: 357 G: 696 B: 455 C: 1543  
Color Temp: 5574 K - Lux: 649 - R: 357 G: 696 B: 455 C: 1543  
Color Temp: 5579 K - Lux: 648 - R: 357 G: 695 B: 455 C: 1543  
Color Temp: 5579 K - Lux: 648 - R: 357 G: 695 B: 455 C: 1543  
Color Temp: 5574 K - Lux: 649 - R: 357 G: 696 B: 455 C: 1544  
Color Temp: 5585 K - Lux: 648 - R: 356 G: 695 B: 455 C: 1542
