tamran/Team-Hydra-II/2-3-17/colorTest_g_20ppm.txt

Color Temp: 5372 K - Lux: 374 - R: 278 G: 432 B: 296 C: 1037  
Color Temp: 5470 K - Lux: 488 - R: 324 G: 547 B: 369 C: 1273  
Color Temp: 5451 K - Lux: 509 - R: 342 G: 572 B: 386 C: 1336  
Color Temp: 5468 K - Lux: 499 - R: 326 G: 557 B: 374 C: 1293  
Color Temp: 5477 K - Lux: 493 - R: 317 G: 548 B: 367 C: 1266  
Color Temp: 5510 K - Lux: 483 - R: 304 G: 535 B: 358 C: 1230  
Color Temp: 5453 K - Lux: 513 - R: 341 G: 575 B: 387 C: 1340  
Color Temp: 5498 K - Lux: 502 - R: 327 G: 561 B: 378 C: 1303  
Color Temp: 5676 K - Lux: 436 - R: 241 G: 471 B: 313 C: 1052  
Color Temp: 5693 K - Lux: 430 - R: 233 G: 463 B: 307 C: 1028  
Color Temp: 5688 K - Lux: 430 - R: 235 G: 464 B: 308 C: 1033  
Color Temp: 5648 K - Lux: 444 - R: 252 G: 482 B: 321 C: 1082  
Color Temp: 5559 K - Lux: 469 - R: 287 G: 517 B: 346 C: 1181  
Color Temp: 5472 K - Lux: 509 - R: 336 G: 570 B: 384 C: 1327  
Color Temp: 5468 K - Lux: 511 - R: 337 G: 572 B: 385 C: 1334  
Color Temp: 5470 K - Lux: 512 - R: 338 G: 573 B: 386 C: 1335  
Color Temp: 5490 K - Lux: 511 - R: 336 G: 572 B: 386 C: 1333  
Color Temp: 5545 K - Lux: 483 - R: 300 G: 534 B: 358 C: 1225  
Color Temp: 5514 K - Lux: 493 - R: 314 G: 548 B: 368 C: 1264  
Color Temp: 5541 K - Lux: 480 - R: 299 G: 531 B: 356 C: 1219  
Color Temp: 5614 K - Lux: 444 - R: 254 G: 482 B: 320 C: 1084  
Color Temp: 5578 K - Lux: 460 - R: 274 G: 504 B: 336 C: 1146  
Color Temp: 5511 K - Lux: 489 - R: 310 G: 543 B: 364 C: 1252  
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
Color Temp: 5574 K - Lux: 550 - R: 335 G: 606 B: 406 C: 1382  
Color Temp: 5566 K - Lux: 549 - R: 335 G: 605 B: 405 C: 1382  
Color Temp: 5566 K - Lux: 549 - R: 335 G: 605 B: 405 C: 1382  
Color Temp: 5574 K - Lux: 550 - R: 335 G: 606 B: 406 C: 1383  
Color Temp: 5574 K - Lux: 550 - R: 335 G: 606 B: 406 C: 1382  
Color Temp: 5566 K - Lux: 549 - R: 335 G: 605 B: 405 C: 1382  
Color Temp: 5566 K - Lux: 549 - R: 335 G: 605 B: 405 C: 1382  
Color Temp: 5574 K - Lux: 550 - R: 335 G: 606 B: 406 C: 1383  
Color Temp: 5574 K - Lux: 550 - R: 335 G: 606 B: 406 C: 1383  
Color Temp: 5574 K - Lux: 550 - R: 335 G: 606 B: 406 C: 1383
