tamran/Team-Hydra-II/2-3-17/colorTest_g_40ppm.txt

Color Temp: 5653 K - Lux: 543 - R: 337 G: 604 B: 411 C: 1384  
Color Temp: 5661 K - Lux: 543 - R: 337 G: 605 B: 412 C: 1385  
Color Temp: 5661 K - Lux: 543 - R: 337 G: 605 B: 412 C: 1385  
Color Temp: 5661 K - Lux: 543 - R: 337 G: 605 B: 412 C: 1385  
Color Temp: 5661 K - Lux: 543 - R: 337 G: 605 B: 412 C: 1385  
Color Temp: 5661 K - Lux: 543 - R: 337 G: 605 B: 412 C: 1385  
Color Temp: 5661 K - Lux: 543 - R: 337 G: 605 B: 412 C: 1385  
Color Temp: 5661 K - Lux: 543 - R: 337 G: 605 B: 412 C: 1385  
Color Temp: 5661 K - Lux: 543 - R: 337 G: 605 B: 412 C: 1385  
Color Temp: 5661 K - Lux: 543 - R: 337 G: 605 B: 412 C: 1385  
Color Temp: 5661 K - Lux: 543 - R: 337 G: 605 B: 412 C: 1385  
Color Temp: 5646 K - Lux: 544 - R: 337 G: 605 B: 411 C: 1384  
Color Temp: 5646 K - Lux: 544 - R: 337 G: 605 B: 411 C: 1384  
Color Temp: 5661 K - Lux: 543 - R: 337 G: 605 B: 412 C: 1385  
Color Temp: 5661 K - Lux: 543 - R: 337 G: 605 B: 412 C: 1385  
Color Temp: 5646 K - Lux: 544 - R: 337 G: 605 B: 411 C: 1384  
Color Temp: 5646 K - Lux: 544 - R: 337 G: 605 B: 411 C: 1384  
Color Temp: 5661 K - Lux: 543 - R: 337 G: 605 B: 412 C: 1385  
Color Temp: 5661 K - Lux: 543 - R: 337 G: 605 B: 412 C: 1385  
Color Temp: 5661 K - Lux: 543 - R: 337 G: 605 B: 412 C: 1384  
Color Temp: 5661 K - Lux: 543 - R: 337 G: 605 B: 412 C: 1385  
Color Temp: 5661 K - Lux: 543 - R: 337 G: 605 B: 412 C: 1385  
Color Temp: 5661 K - Lux: 543 - R: 337 G: 605 B: 412 C: 1385  
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
Color Temp: 5623 K - Lux: 502 - R: 326 G: 565 B: 387 C: 1312  
Color Temp: 5623 K - Lux: 502 - R: 326 G: 565 B: 387 C: 1311  
Color Temp: 5621 K - Lux: 502 - R: 325 G: 564 B: 386 C: 1308  
Color Temp: 5621 K - Lux: 502 - R: 325 G: 564 B: 386 C: 1308  
Color Temp: 5621 K - Lux: 502 - R: 325 G: 564 B: 386 C: 1309  
Color Temp: 5621 K - Lux: 502 - R: 325 G: 564 B: 386 C: 1309  
Color Temp: 5621 K - Lux: 502 - R: 325 G: 564 B: 386 C: 1309  
Color Temp: 5621 K - Lux: 502 - R: 325 G: 564 B: 386 C: 1309  
Color Temp: 5621 K - Lux: 502 - R: 325 G: 564 B: 386 C: 1309  
Color Temp: 5621 K - Lux: 502 - R: 325 G: 564 B: 386 C: 1309
