tamran/Team-Hydra-II/2-3-17/colorTest_g_ambient.txt

Color Temp: 5442 K - Lux: 515 - R: 330 G: 571 B: 380 C: 1330  
Color Temp: 5442 K - Lux: 515 - R: 330 G: 571 B: 380 C: 1331  
Color Temp: 5445 K - Lux: 510 - R: 326 G: 565 B: 376 C: 1315  
Color Temp: 5456 K - Lux: 508 - R: 324 G: 563 B: 375 C: 1310  
Color Temp: 5445 K - Lux: 510 - R: 326 G: 565 B: 376 C: 1316  
Color Temp: 5446 K - Lux: 513 - R: 329 G: 569 B: 379 C: 1326  
Color Temp: 5446 K - Lux: 513 - R: 329 G: 569 B: 379 C: 1326  
Color Temp: 5446 K - Lux: 513 - R: 329 G: 569 B: 379 C: 1327  
Color Temp: 5448 K - Lux: 514 - R: 330 G: 570 B: 380 C: 1328  
Color Temp: 5448 K - Lux: 514 - R: 330 G: 570 B: 380 C: 1328  
Color Temp: 5448 K - Lux: 514 - R: 330 G: 570 B: 380 C: 1328  
Color Temp: 5448 K - Lux: 514 - R: 330 G: 570 B: 380 C: 1328  
Color Temp: 5448 K - Lux: 514 - R: 330 G: 570 B: 380 C: 1328  
Color Temp: 5448 K - Lux: 514 - R: 330 G: 570 B: 380 C: 1328  
Color Temp: 5433 K - Lux: 515 - R: 330 G: 570 B: 379 C: 1327  
Color Temp: 5433 K - Lux: 515 - R: 330 G: 570 B: 379 C: 1328  
Color Temp: 5448 K - Lux: 514 - R: 330 G: 570 B: 380 C: 1328  
Color Temp: 5448 K - Lux: 514 - R: 330 G: 570 B: 380 C: 1328  
Color Temp: 5446 K - Lux: 513 - R: 329 G: 569 B: 379 C: 1327  
Color Temp: 5446 K - Lux: 513 - R: 329 G: 569 B: 379 C: 1327  
Color Temp: 5448 K - Lux: 514 - R: 330 G: 570 B: 380 C: 1328  
Color Temp: 5448 K - Lux: 514 - R: 330 G: 570 B: 380 C: 1328  
Color Temp: 5433 K - Lux: 515 - R: 330 G: 570 B: 379 C: 1328  
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
Color Temp: 5455 K - Lux: 514 - R: 329 G: 570 B: 380 C: 1328  
Color Temp: 5448 K - Lux: 514 - R: 330 G: 570 B: 380 C: 1329  
Color Temp: 5448 K - Lux: 514 - R: 330 G: 570 B: 380 C: 1329  
Color Temp: 5455 K - Lux: 514 - R: 329 G: 570 B: 380 C: 1328
